eadpucv/actor-reactor/processing/signo/application.linux-armv6hf/source/words.pde

String[] spanish = {"américa","árbol","libertad","empatía","palma","viento","ave","pensamiento","perseverancia","sueño","grito","salto","sol","narval","cualquiera","sueños","gato","armonía","mar","autóctono","piedra","red","visión","subjetivo","no","flor","belleza","efímero","teatro","aire","flecha","confianza","paz","zoperútano","paciencia","diseño","expresión","ascendente","pintura","travesía","lluvia","estrellas","caracol","nervio","cielo","acción","espacio","beso","nobleza","idea","luz ","ilusión","armonía","esfuerzo","luz","flor","luz","paz","crea","inventar","libre","sobra","niño","nuevo","amor","sol","renacer","creación","felicidad","mirada","flor","lejos","libertad","sol","dedicación","justo","suerte","luz","luz","aire","sueño","árbol","respeto","vida","universo","cielo","esperanza","nuevo","serenidad","felicidad","mar","pánico","nube","poesía","fuego","vida","justicia","Anglo","esperanza","vida","piano","sol","esfuerzo","familia","lucha","verso","contigo","árbol","flora","luna","esperanza","vida","altura","amabilidad","naturaleza","sol","sueño","camino","expresión","odisea","ideas","cambio","nuevo","andar","tonto","origen","noche","libertad","expansión","híbrida","la bandada","asincronía","elevada","el aro","fragmentar","la extensión","el cuerpo","descalce","ampliación","los perfiles","impulso","acorazado","el valle","elegancia","segmentada","el puño","vínculo","sinuoso","la flor","arritmia","dispar","el vuelo","distensión","palpitar","el pez"};
String[] english = {"America","tree","freedom","empathy","palm","wind","bird","thought","perseverance","dream","scream","jump","Sun","narwhal","anyone","dreams","cat","harmony","sea","indigenous","stone","net","view","subjective","do not","flower","beauty","ephemeral","theater","air","arrow","trust","peace","fool","patience","design","expression","upward","painting","crossing","rain","Stars","snail","nerve","heaven","action","space","kiss","nobility","idea","light","delusion","harmony","effort","light","flower","light","peace","creates","invent","free","surplus","boy","new","love","Sun","be reborn","creation","happiness","look","flower","far","freedom","Sun","dedication","fair","luck","light","light","air","dream","tree","respect","lifetime","universe","heaven","hope","new","serenity","happiness","sea","panic","cloud","poetry","fire","life","justice","Anglo","hope","lifetime","piano","Sun","effort","family","fight","verse","with you","tree","flora","Moon","hope","lifetime","height","amiability","nature","Sun","dream","path","expression","Odyssey","Ideas","change","new","walk","fool","origin","night","freedom","expansion","hybrid","the flock","asynchrony","high","ring","to fragment","the extension","the body","misalignment","extension","the profiles","impulse","battleship","Valley","elegance","segmented","the fist","link","sinuous","the flower","arrhythmia","disparate","the flight","distension","throb","the fish"};
String[] german = {"Amerika","Baum","Freiheit","Empathie","Palme","Wind","Vogel","Denken","Ausdauer","Traum","Schrei","springen","Sonne","Narwal","jeder","Träume","Katze","Harmonie","Meer","autochthonen","Stein","Netzwerk","Ansicht","subjektiv","keine","Blume","Schönheit","kurzlebig","Theater","Luft","Pfeil","Vertrauen","Frieden","Dummkopf","Geduld","Design","Ausdruck","nach oben","Malerei","Kreuzung","regen","Sterne","Schnecke","Nerv","Himmel","Aktion","Raum","Kuss","Adel","Idee","Licht","Hoffnung","Harmonie","Anstrengung","Licht","Blume","Licht","Frieden","schafft","erfinden","kostenlos","Überschuss","Kind","neu","liebe","Sonne","wiedergeboren","Schaffung","Glück","aussehen","Blume","weit","Freiheit","Sonne","Widmung","Recht","Glück","Licht","Licht","Luft","Traum","Baum","Respekt","Leben","Universum","Himmel","Hoffnung","neu","Gelassenheit","Glück","Meer","Panik","Wolke","Poesie","Feuer","Leben","Gerechtigkeit","Anglo","Hoffnung","Leben","Klavier","Sonne","Anstrengung","Familie","Kampf","Vers","mit Ihnen","Baum","Flora","Mond","Hoffnung","Leben","Höhe","Freundlichkeit","Natur","Sonne","Traum","Weg","Ausdruck","Odyssee","Ideen","Veränderung","neu","gehen","albern","Quelle","Nacht","Freiheit","Erweiterung","Hybrid","die Herde","Asynchronität","hoch","der Ring","fragmentieren","die Erweiterung","der Körper","Fehlausrichtung","Erweiterung","die Profile","Impuls","gepanzert","das Tal","Eleganz","segmentiert","die Faust","Link","gewunden","die Blume","Herzrhythmusstörungen","dispar","der Flug","aufgebläht","pochen","der Fisch"};
String[] greek = {"Αμερική","δέντρο","ελευθερία","ενσυναίσθηση,συμπάθεια","παλάμη","άνεμος","πουλί","σκέψη","επιμονή","όνειρο","κραυγή","άλμα","ήλιος","μονόδοντος φάλαινα","κάθενας ","όνειρα","γάτα","αρμονία","θάλασσα","αυτόχθων","πέτρα","δίκτυο","θέα","υποκειμενικός","όχι","λουλούδι","ομορφιά","εφήμερο","θέατρο","αέρας","βέλος","εμπιστοσύνη","ειρήνη","ανόητος","υπομονή","σχέδιο","έκφραση","επάνω","ζωγραφική","διάβαση","βροχή","αστέρια","σαλιγκάρι","νεύρο","ουρανός","δράση","χώρος","φιλί","αρχοντιά","ιδέα","φως","αυταπάτη","αρμονία","προσπάθεια","φως","λουλούδι","φως","ειρήνη","δημιουργεί","εφευρίσκω","ελεύθερο","πλεόνασμα","παιδί","νέος","αγάπη","ήλιος","να ξαναγεννηθεί","δημιουργία","ευτυχία","ματιά","λουλούδι","μακριά","ελευθερία","ήλιος","αφιέρωση","δεξιά","τύχη","φως","φως","αέρας","όνειρο","δέντρο","σεβασμός","ζωή","σύμπαν","ουρανός","ελπίδα","νέος","γαλήνη","ευτυχία","θάλασσα","πανικός","σύννεφο","ποίηση","φωτιά","ζωή","δικαιοσύνη","Anglo","ελπίδα","ζωή","πιάνο","ήλιος","προσπάθεια","οικογένεια","πάλη","στίχος","μαζί σου","δέντρο","χλωρίδα","φεγγάρι","ελπίδα","ζωή","ύψος","καλοσύνη","φύση","ήλιος","όνειρο","μονοπάτι","έκφραση","Οδύσσεια","ιδέες","αλλαγή","νέος","βόλτα","ανόητος","πηγή","νύχτα","ελευθερία","επέκταση","υβριδικό","το κοπάδι","ασύγχρονη","ψηλά","το δαχτυλίδι","να αποσπαστεί","την επέκταση","το σώμα","εσφαλμένη ευθυγράμμιση","μεγέθυνση","τα προφίλ","ώθηση","θωρακισμένο","την κοιλάδα","κομψότητα","κατακερματισμένη","η γροθιά","σύνδεσμο","ελικοειδής","το λουλούδι","αρρυθμία","να εξαφανιστεί","την πτήση","φούσκωμα","παλμός","τα ψάρια"};
String[] french = {"amérique","arbre","liberté","empathie","palme","vent","oiseau","penser","persévérance","rêve","crier","sauter","soleil","narval","tout","rêves","chat","harmonie","mer","autochtone","la pierre","rouge","vision","subjectif","non","fleur","beauté","éphémère","théâtre","air","flèche","confiance","la paix","zoperutano","patience","conception","expression","ascendant","peinture","croisement","pluie","étoiles","escargot","nerf","le paradis","action","l'espace","baiser","noblesse","idée","lumière","illusion","harmonie","effort","lumière","fleur","lumière","la paix","crée","inventer","libre","restes","enfant","nouveau","amour","soleil","renaître","création","félicité","regarder","fleur","loin","liberté","soleil","dévouement","juste","la chance","lumière","lumière","air","rêve","arbre","le respect","vie","univers","le paradis","l'espoir","nouveau","sérénité","félicité","mer","panique","nuage","poésie","le feu","vie","justice","Anglo","l'espoir","vie","piano","soleil","effort","famille","combattre","verset","avec vous","arbre","flore","lune","l'espoir","vie","hauteur","gentillesse","la nature","soleil","rêve","route","expression","odyssée","idées","changer","nouveau","marcher","imbécile","source","nuit","liberté","expansion","hybride","le troupeau","asynchronie","élevé","l'anneau","se fragmenter","l'extension","le corps","désalignement","élargissement","les profils","impulsion","blindé","la vallée","élégance","segmenté","le poing","lien","sinueux","la fleur","arythmie","dispar","le vol","ballonnement","palpiter","le poisson"};
