eadpucv/actor-reactor/expo/processing/signo_cards/words.pde

String[] spanish = {"acción", "aire", "alba", "américa", "amor", "árbol", "árbol", "armonía", "ascendente", "autóctono", "ave", "belleza", "beso", "camino", "caracol", "cielo", "confianza", "conyo", "crea", "creación", "crónica", "cualquiera", "dedicación", "diseño", "efímero", "el acto", "el camino", "el desconocido", "el guión", "el océano", "el oficio", "el rito", "el signo", "empatía", "esfuerzo", "espacio", "esperanza", "estrellas", "expresión", "felicidad", "flecha", "flor", "fuego", "gato", "grito", "hombres libres", "idea", "ilusión", "inventar", "justicia", "justo", "la extensión", "la fiesta", "la heredad", "la muerte", "la piedad", "la torre", "la tradición", "lejos", "libertad", "libre", "lluvia", "los nueve", "luz ", "mar", "medidas", "memoria", "mirada", "narval", "nervio", "niño", "no", "nobleza", "nube", "nuevo", "ocaso", "paciencia", "palacio", "palma", "pánico", "paz", "pensamiento", "perseverancia", "piano", "piedra", "pintura", "poesía", "red", "renacer", "respeto", "salto", "serenidad", "sobra", "sol", "subjetivo", "sueño", "sueños", "suerte", "teatro", "torre", "travesía", "universo", "vida", "viento", "visión", "zoperútano"};
String[] english = {"action", "air", "sunrise", "America", "love", "tree", "tree", "harmony", "upward", "indigenous", "bird", "beauty", "kiss", "path", "snail", "heaven", "trust", "with me", "creates", "creation", "chronicle", "anyone", "dedication", "design", "ephemeral", "the act", "the road", "the unknown", "the script", "the ocean", "The office", "the rite", "The sign", "empathy", "effort", "space", "hope", "Stars", "expression", "happiness", "arrow", "flower", "fire", "cat", "scream", "Free men", "idea", "delusion", "invent", "justice", "fair", "the extension", "Party", "The inheritance", "death", "The piety", "tower", "the tradition", "far", "freedom", "free", "rain", "The nine", "light", "sea", "measurements", "memory", "look", "narwhal", "nerve", "boy", "do not", "nobility", "cloud", "new", "sunset", "patience", "palace", "palm", "panic", "peace", "thought", "perseverance", "piano", "stone", "painting", "poetry", "net", "be reborn", "respect", "jump", "serenity", "surplus", "Sun", "subjective", "dream", "dreams", "luck", "theater", "tower", "crossing", "universe", "life", "wind", "view", "fool"};
String[] german = {"Aktion", "Luft", "Dawn", "Amerika", "liebe", "Baum", "Baum", "Harmonie", "nach oben", "autochthonen", "Vogel", "Schönheit", "Kuss", "Path", "Schnecke", "Himmel", "Vertrauen", "mit I", "schafft", "Schaffung", "Chronische", "jeder", "Widmung", "Design", "kurzlebig", "Der Akt", "die Art und Weise", "unbekannt", "das Skript", "das Meer", "das Büro", "der Ritus", "Zeichen", "Empathie", "Anstrengung", "Space", "Hoffnung", "Sterne", "Ausdruck", "Glück", "Pfeil", "Blume", "Feuer", "Katze", "Schrei", "Freemen", "Idee", "Hoffnung", "erfinden", "Gerechtigkeit", "Recht", "Extension", "die Partei", "Vererbung", "Tod", "Piety", "Turm", "Tradition", "weit", "Freiheit", "kostenlos", "regen", "Nine", "Licht", "Meer", "Maßnahmen", "Memory", "aussehen", "Narwal", "Nerv", "Kind", "keine", "Adel", "Wolke", "neu", "Twilight", "Geduld", "Palace", "Palme", "Panik", "Frieden", "Denken", "Ausdauer", "Piano", "Stein", "Malerei", "Poesie", "Netzwerk", "wiedergeboren", "Respekt", "springen", "Gelassenheit", "Überschuss", "Sonne", "subjektiv", "Traum", "Träume", "Glück", "Theater", "Tower", "Kreuzung", "Universum", "Leben", "Wind", "Ansicht", "Dummkopf"};
String[] greek = {"δράση", "αέρας", "Αυγή", "Αμερική", "αγάπη", "δέντρο", "δέντρο", "αρμονία", "επάνω", "αυτόχθων", "πουλί", "ομορφιά", "φιλί", "Διαδρομή", "σαλιγκάρι", "ουρανός", "εμπιστοσύνη", "με Ι", "δημιουργεί", "δημιουργία", "Χρόνια", "κάθε", "αφιέρωση", "σχέδιο", "εφήμερος", "Η πράξη", "ο τρόπος", "άγνωστος", "το σενάριο", "ο ωκεανός", "το γραφείο", "η ιεροτελεστία", "σήμα", "ενσυναίσθηση", "προσπάθεια", "Διάστημα", "ελπίδα", "αστέρια", "έκφραση", "ευτυχία", "βέλος", "λουλούδι", "φωτιά", "γάτα", "κραυγή", "Ελεύθεροι", "ιδέα", "ελπίδα", "εφευρίσκω", "δικαιοσύνη", "δεξιά", "Επέκταση", "το κόμμα", "Κληρονομιά", "θάνατος", "Ευσέβεια", "πύργος", "παράδοση", "μακριά", "ελευθερία", "δωρεάν", "βροχή", "Εννέα", "φως", "θάλασσα", "Μέτρα", "Μνήμη", "ματιά", "μονόκερως", "νεύρο", "παιδί", "όχι", "αρχοντιά", "σύννεφο", "νέος", "λυκόφως", "υπομονή", "Παλάτι", "παλάμη", "πανικός", "ειρήνη", "σκέψη", "επιμονή", "Λίρα", "πέτρα", "ζωγραφική", "ποίηση", "δίκτυο", "να ξαναγεννηθεί", "σεβασμός", "άλμα", "γαλήνη", "πλεόνασμα", "ήλιος", "υποκειμενικός", "όνειρο", "όνειρα", "τύχη", "θέατρο", "Πύργος", "διάβαση", "σύμπαν", "ζωή", "άνεμος", "θέα", "ανόητος"};
