eadpucv/actor-reactor/arduino/expo-units/otras/ac_expo_s05/send_data.ino

/*
 *  arduino - puredata communication
 *  
 */

void send_data() {
  OSCMessage msg("/bang/s08");
  msg.add((float)normalize);
  wifiLink.println("AT+CIPSEND=4,16");
  wifiLink.find(">");
  msg.send(wifiLink);
  msg.empty();
}
