eadpucv/actor-reactor/arduino/expo-units/otras/ac_expo_s01/ac_units.ino

/**

  "Vínculo Sinuoso"         s01     Javier, César

  "Descalce Ampliado"       s02     Catalina C, Bastián

  "Expansión Híbrida"       s03     Consuelo, Melisa, Carolina

  "Arritmia Dispar"         s04     Doyma, Javiera

  "Fragmentada Extensión"   s05     Bastián M, Monserrat

  "Asincronía Elevada"      s06     MªIgnacia, Sofía S, Paul, Sam

  "Impulso Acorazado"       s07     Alejandro, Dominique, Javier

  "Elegancia Segmentada"    s08     Consuelo, Marcelo

  "Distensión Palpitante"   s09     Sofía V. Catalina M.

*/
