eadpucv/actor-reactor/processing/signo/application.linux-armv6hf/source/Obj_Point.pde

class Point {
  int seed;
  float amp, zoom;
  float x, y, t, s; // x,y, angle and step
  
  Point(float x, float y) {
    this.x = x;
    this.y = y;
    t = random(TWO_PI);
    s = random(.2, 1);
    
    seed = round(random(100000));
    amp = random(1, 3);
    zoom = random(3000, 10000);
  }

  void move() {
    
    noiseSeed(seed);
    float dif = .5 - noise((float)millis()/zoom) * amp;
    t += dif;
    
    x += cos(t)*s;
    y += sin(t)*s;
  }
}
