eadpucv/actor-reactor/arduino/tests/Blocking/Blocking.ino

// Blocking.pde
// -*- mode: C++ -*-
//
// Shows how to use the blocking call runToNewPosition
// Which sets a new target position and then waits until the stepper has 
// achieved it.
//
// Copyright (C) 2009 Mike McCauley
// $Id: Blocking.pde,v 1.1 2011/01/05 01:51:01 mikem Exp mikem $

#include <AccelStepper.h>

//AccelStepper stepper(AccelStepper::DRIVER, 9, 8); // CLK+(paso) -> pin 8 --- CW+(direccion) -> pin 9
AccelStepper stepper(2, 9, 8); 


void setup(){  
  Serial.begin(57600);
  stepper.setMaxSpeed(10000.0);
  stepper.setSpeed(9000);
  stepper.setAcceleration(1000);
}

int range = 8000;

void loop()
{    
    Serial.println("moviendo...");
    stepper.runToNewPosition(range);
    delay(500);
    stepper.runToNewPosition(-range);
    Serial.println("terminando...");
    delay(500);
}
