eadpucv/actor-reactor/arduino/tests/ESP8266sendMessage/ESP8266sendMessage.ino

#include <ESP8266WiFi.h>
#include <ESP8266WiFiAP.h>
#include <ESP8266WiFiGeneric.h>
#include <ESP8266WiFiMulti.h>
#include <ESP8266WiFiScan.h>
#include <ESP8266WiFiSTA.h>
#include <ESP8266WiFiType.h>
#include <WiFiClient.h>
#include <WiFiClientSecure.h>
#include <WiFiServer.h>
#include <WiFiUdp.h>

/*---------------------------------------------------------------------------------------------

  Open Sound Control (OSC) library for the ESP8266

  Example for sending messages from the ESP8266 to a remote computer
  The example is sending "hello, osc." to the address "/test".

  This example code is in the public domain.

--------------------------------------------------------------------------------------------- */
#include <ESP8266WiFi.h>
#include <WiFiUdp.h>
#include <OSCMessage.h>

char ssid[] = "AC";                         // your network SSID (name)
char pass[] = "actor-reactor";              // your network password

WiFiUDP Udp;                                // A UDP instance to let us send and receive packets over UDP
const IPAddress outIp(10,40,10,105);        // remote IP of your computer
const unsigned int outPort = 9999;          // remote port to receive OSC
const unsigned int localPort = 8888;        // local port to listen for OSC packets (actually not used for sending)

void setup() {
    Serial.begin(115200);

    // Connect to WiFi network
    Serial.println();
    Serial.println();
    Serial.print("Connecting to ");
    Serial.println(ssid);
    WiFi.begin(ssid, pass);

    while (WiFi.status() != WL_CONNECTED) {
        delay(500);
        Serial.print(".");
    }
    Serial.println("");

    Serial.println("WiFi connected");
    Serial.println("IP address: ");
    Serial.println(WiFi.localIP());

    Serial.println("Starting UDP");
    Udp.begin(localPort);
    Serial.print("Local port: ");
    Serial.println(Udp.localPort());

}

void loop() {
    OSCMessage msg("/test");
    msg.add("hello, osc.");
    Udp.beginPacket(outIp, outPort);
    msg.send(Udp);
    Udp.endPacket();
    msg.empty();
    delay(500);
}
